filoden/Nixie_Clock_STM32/Current Iteration/Src/Core/Src/spi.c

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
/* Includes ------------------------------------------------------------------*/
#include "spi.h"

/* USER CODE BEGIN 0 */
#include <stdlib.h>
#include <string.h>
#include "FATFS_SD.h"
extern uint16_t Timer1;
extern uint16_t Timer2;


/* USER CODE END 0 */

SPI_HandleTypeDef hspi1;
DMA_HandleTypeDef hdma_spi1_rx;
DMA_HandleTypeDef hdma_spi1_tx;

/* SPI1 init function */
void MX_SPI1_Init(void)
{

  hspi1.Instance = SPI1;
  hspi1.Init.Mode = SPI_MODE_MASTER;
  hspi1.Init.Direction = SPI_DIRECTION_2LINES;
  hspi1.Init.DataSize = SPI_DATASIZE_8BIT;
  hspi1.Init.CLKPolarity = SPI_POLARITY_LOW;
  hspi1.Init.CLKPhase = SPI_PHASE_1EDGE;
  hspi1.Init.NSS = SPI_NSS_SOFT;
  hspi1.Init.BaudRatePrescaler = SPI_BAUDRATEPRESCALER_4;
  hspi1.Init.FirstBit = SPI_FIRSTBIT_MSB;
  hspi1.Init.TIMode = SPI_TIMODE_DISABLE;
  hspi1.Init.CRCCalculation = SPI_CRCCALCULATION_DISABLE;
  hspi1.Init.CRCPolynomial = 7;
  hspi1.Init.CRCLength = SPI_CRC_LENGTH_DATASIZE;
  hspi1.Init.NSSPMode = SPI_NSS_PULSE_DISABLE;
  if (HAL_SPI_Init(&hspi1) != HAL_OK)
  {
    Error_Handler();
  }
}

void HAL_SPI_MspInit(SPI_HandleTypeDef* spiHandle)
{

  GPIO_InitTypeDef GPIO_InitStruct = {0};
  if(spiHandle->Instance==SPI1)
  {
    /* SPI1 clock enable */
    __HAL_RCC_SPI1_CLK_ENABLE();

    __HAL_RCC_GPIOA_CLK_ENABLE();
    __HAL_RCC_GPIOB_CLK_ENABLE();
    /**SPI1 GPIO Configuration
    PA5     ------> SPI1_SCK
    PA12 [PA10]     ------> SPI1_MOSI
    PB4     ------> SPI1_MISO
    */
    GPIO_InitStruct.Pin = GPIO_PIN_5;
    GPIO_InitStruct.Mode = GPIO_MODE_AF_PP;
    GPIO_InitStruct.Pull = GPIO_PULLDOWN;
    GPIO_InitStruct.Speed = GPIO_SPEED_FREQ_LOW;
    GPIO_InitStruct.Alternate = GPIO_AF0_SPI1;
    HAL_GPIO_Init(GPIOA, &GPIO_InitStruct);

    GPIO_InitStruct.Pin = GPIO_PIN_12;
    GPIO_InitStruct.Mode = GPIO_MODE_AF_PP;
    GPIO_InitStruct.Pull = GPIO_PULLUP;
    GPIO_InitStruct.Speed = GPIO_SPEED_FREQ_LOW;
    GPIO_InitStruct.Alternate = GPIO_AF0_SPI1;
    HAL_GPIO_Init(GPIOA, &GPIO_InitStruct);

    GPIO_InitStruct.Pin = GPIO_PIN_4;
    GPIO_InitStruct.Mode = GPIO_MODE_AF_PP;
    GPIO_InitStruct.Pull = GPIO_PULLUP;
    GPIO_InitStruct.Speed = GPIO_SPEED_FREQ_LOW;
    GPIO_InitStruct.Alternate = GPIO_AF0_SPI1;
    HAL_GPIO_Init(GPIOB, &GPIO_InitStruct);

    /* SPI1 DMA Init */
    /* SPI1_RX Init */
    hdma_spi1_rx.Instance = DMA1_Channel1;
    hdma_spi1_rx.Init.Request = DMA_REQUEST_SPI1_RX;
    hdma_spi1_rx.Init.Direction = DMA_PERIPH_TO_MEMORY;
    hdma_spi1_rx.Init.PeriphInc = DMA_PINC_DISABLE;
    hdma_spi1_rx.Init.MemInc = DMA_MINC_ENABLE;
    hdma_spi1_rx.Init.PeriphDataAlignment = DMA_PDATAALIGN_BYTE;
    hdma_spi1_rx.Init.MemDataAlignment = DMA_MDATAALIGN_BYTE;
    hdma_spi1_rx.Init.Mode = DMA_NORMAL;
    hdma_spi1_rx.Init.Priority = DMA_PRIORITY_HIGH;
    if (HAL_DMA_Init(&hdma_spi1_rx) != HAL_OK)
    {
      Error_Handler();
    }

    __HAL_LINKDMA(spiHandle,hdmarx,hdma_spi1_rx);

    /* SPI1_TX Init */
    hdma_spi1_tx.Instance = DMA1_Channel2;
    hdma_spi1_tx.Init.Request = DMA_REQUEST_SPI1_TX;
    hdma_spi1_tx.Init.Direction = DMA_MEMORY_TO_PERIPH;
    hdma_spi1_tx.Init.PeriphInc = DMA_PINC_DISABLE;
    hdma_spi1_tx.Init.MemInc = DMA_MINC_ENABLE;
    hdma_spi1_tx.Init.PeriphDataAlignment = DMA_PDATAALIGN_BYTE;
    hdma_spi1_tx.Init.MemDataAlignment = DMA_MDATAALIGN_BYTE;
    hdma_spi1_tx.Init.Mode = DMA_NORMAL;
    hdma_spi1_tx.Init.Priority = DMA_PRIORITY_MEDIUM;
    if (HAL_DMA_Init(&hdma_spi1_tx) != HAL_OK)
    {
      Error_Handler();
    }

    __HAL_LINKDMA(spiHandle,hdmatx,hdma_spi1_tx);

  }
}

void HAL_SPI_MspDeInit(SPI_HandleTypeDef* spiHandle)
{

  if(spiHandle->Instance==SPI1)
  {
    /* Peripheral clock disable */
    __HAL_RCC_SPI1_CLK_DISABLE();

    /**SPI1 GPIO Configuration
    PA5     ------> SPI1_SCK
    PA12 [PA10]     ------> SPI1_MOSI
    PB4     ------> SPI1_MISO
    */
    HAL_GPIO_DeInit(GPIOA, GPIO_PIN_5|GPIO_PIN_12);

    HAL_GPIO_DeInit(GPIOB, GPIO_PIN_4);

    /* SPI1 DMA DeInit */
    HAL_DMA_DeInit(spiHandle->hdmarx);
    HAL_DMA_DeInit(spiHandle->hdmatx);
  }
}

/* USER CODE BEGIN 1 */

void disk_timerproc(void)
{
  if (Timer1) Timer1--;
  if (Timer2) Timer2--;
}

static uint8_t spi_sd_dummy_tx[512];
static uint8_t spi_sd_dummy_init = 0;


#ifndef HSPI_SDCARD
#define HSPI_SDCARD (&hspi1)
#endif

static volatile uint8_t spi_sd_dma_done = 0;
static volatile uint8_t spi_sd_dma_err  = 0;

// 512 dummy bytes to clock out SD payload reads


static void spi_sd_init_dummy(void)
{
    if (!spi_sd_dummy_init) {
        memset(spi_sd_dummy_tx, 0xFF, sizeof(spi_sd_dummy_tx));
        spi_sd_dummy_init = 1;
    }
}

// Blocking wait wrapper around HAL SPI DMA TxRx
bool spi_sd_txrx_dma(uint8_t *tx, uint8_t *rx, uint16_t n, uint32_t timeout_ms)
{
    uint32_t t0 = HAL_GetTick();
    spi_sd_dma_done = 0;
    spi_sd_dma_err  = 0;

    if (HAL_SPI_TransmitReceive_DMA(HSPI_SDCARD, tx, rx, n) != HAL_OK) {
        return false;
    }

    while (!spi_sd_dma_done && !spi_sd_dma_err) {
        if ((HAL_GetTick() - t0) > timeout_ms) {
            (void)HAL_SPI_Abort(HSPI_SDCARD);
            return false;
        }
    }
    return (spi_sd_dma_err == 0);
}

void HAL_SPI_TxRxCpltCallback(SPI_HandleTypeDef *hspi)
{
    if (hspi == HSPI_SDCARD) {
        spi_sd_dma_done = 1;
    }
}

void HAL_SPI_ErrorCallback(SPI_HandleTypeDef *hspi)
{
    if (hspi == HSPI_SDCARD) {
        spi_sd_dma_err = 1;
    }
}

/* USER CODE END 1 */
