filoden/Nixie_Clock_STM32/Current Iteration/Src/Core/Inc/display.h

/*
 * display.h
 *
 *  Created on: Feb 1, 2026
 *      Author: Apath
 */

#ifndef INC_DISPLAY_H_
#define INC_DISPLAY_H_
#include <stdint.h>

void packageDs(uint16_t data, uint64_t *ds);

void write_LE_N(uint8_t mode);

void write_CLK(uint8_t mode){;

void write_DIN(uint8_t mode);

void write_BL_N(uint8_t mode);

void nixieDisp(uint16_t data);

#endif /* INC_DISPLAY_H_ */
